Laaaarry/3V3-Buck-Converter-PCB/LTspice_Sim/Buck3v3.asc

U1: LMR50410YF_Q1_TRANS
.include LMR50410YF_Q1_TRANS_ltspice.lib
